MOSH-Insa-Toulouse/2025-2026-4GP-ZoeNonon-LouiseLammertyn-JilSaintMartin/1.Photos/Menu_du_capteur.jpg

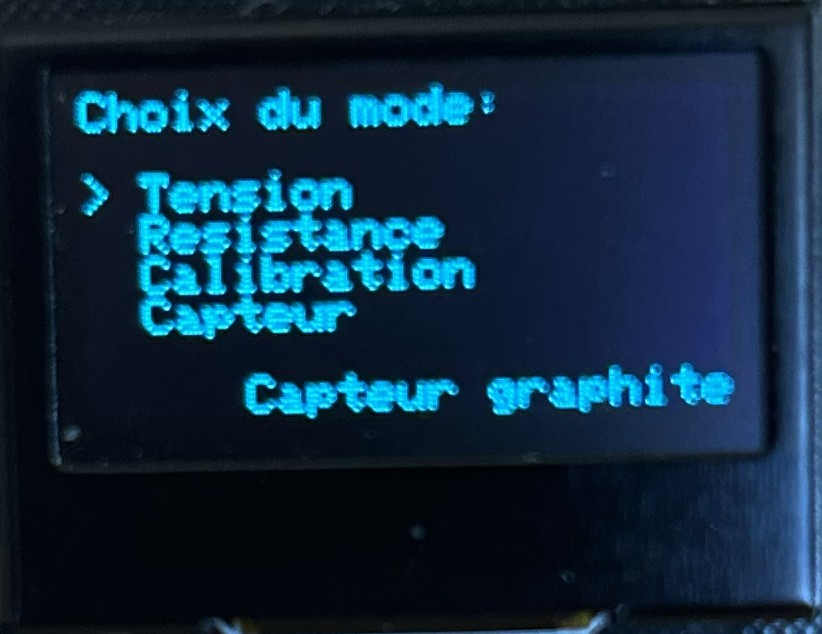
1.Photos/Menu_du_capteur.jpg
