MOSH-Insa-Toulouse/2025-2026-4GP-ZoeNonon-LouiseLammertyn-JilSaintMartin/2.LTSpice/capteur.png

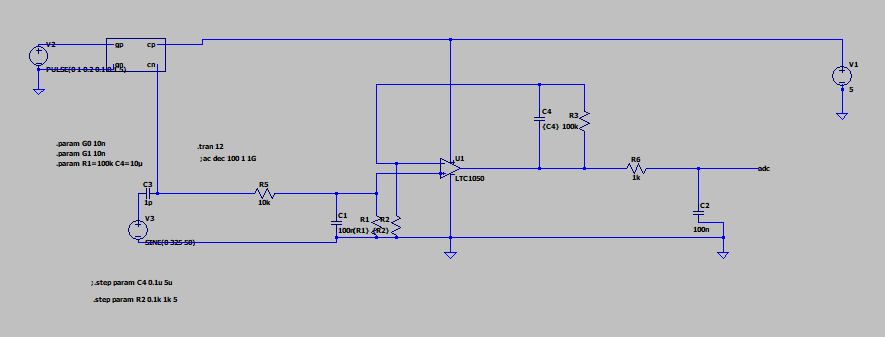
2.LTSpice/capteur.png
