MOSH-Insa-Toulouse/2025-2026-4GP-ZoeNonon-LouiseLammertyn-JilSaintMartin/5.Application/Lien_téléchargement.png

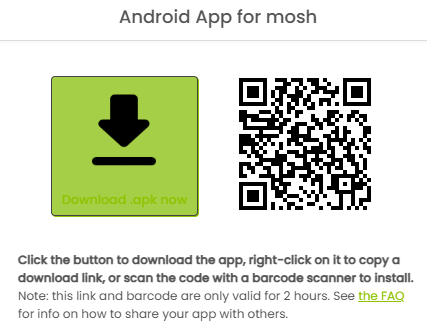
5.Application/Lien_téléchargement.png
