MOSH-Insa-Toulouse/2025-2026-4GP-ZoeNonon-LouiseLammertyn-JilSaintMartin/3.KiCad/Projet_capteur_pcb/Model 3d/pin-header-female-2-54mm-different-pin-numbers-1/10-Pin Header - Female - 2.54mm.step

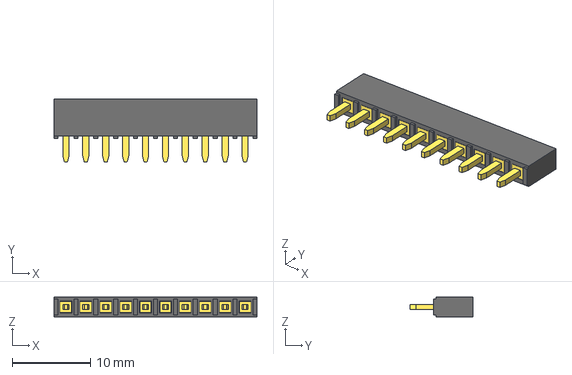
[picture p32: CAD file, 2026-04-08]
3.KiCad/Projet_capteur_pcb/Model 3d/pin-header-female-2-54mm-different-pin-numbers-1/10-Pin Header - Female - 2.54mm.step
25.9 x 8.00 x 2.50 mm
