MOSH-Insa-Toulouse/2025-2026-4GP-ZoeNonon-LouiseLammertyn-JilSaintMartin/1.Photos/Banc_de_test.png

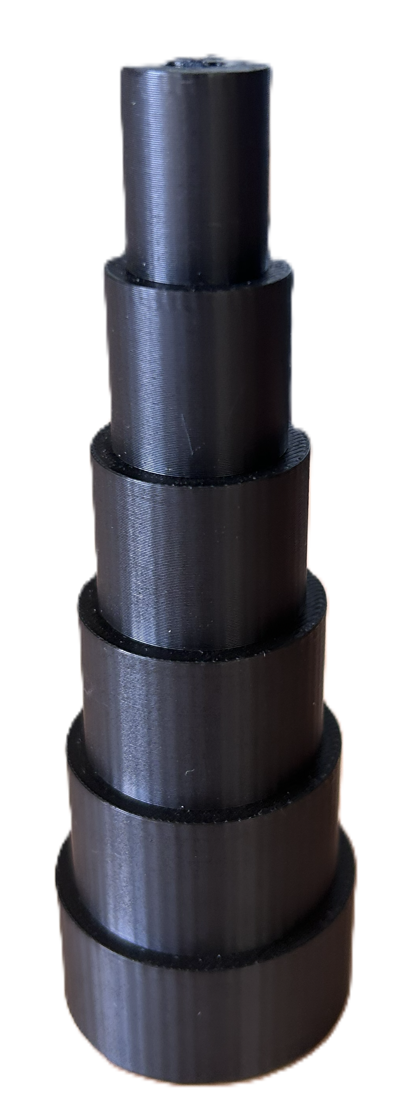
1.Photos/Banc_de_test.png
