MOSH-Insa-Toulouse/2025-2026-4GP-ZoeNonon-LouiseLammertyn-JilSaintMartin/Capteur_graphite.asc

B1: bi; I=v(cp,cn)*({G0}+{G1}*v(gc,gn))
C1: cap; 200µ
R1: res; 1k
Named nets: gp, gn, gc, cp, cn
