MOSH-Insa-Toulouse/2025-2026-4GP-ZoeNonon-LouiseLammertyn-JilSaintMartin/Draft2.asc

C1: cap; 0
C2: cap; 100n
C4: cap; 0
I1: current; PULSE(50n 100n 1 0.1 0.1 2); AC 1
R1: res; 100k
R2: res; 1k
R3: res; 100k
R5: res; 10k
R6: res; 1k
U1: LTC1050
V1: voltage; 5
Named nets: 0, adc
;tran 4
.ac dec 100 1 1G
