MOSH-Insa-Toulouse/2025-2026-4GP-ZoeNonon-LouiseLammertyn-JilSaintMartin/Schéma.asc

C1: cap; 100n
C2: cap; 100n
C3: cap; 1p
C4: cap; {C4}
R1: res; {R1}
R2: res; {R2}
R3: res; 100k
R5: res; 10k
R6: res; 1k
U1: LTC1050
V1: voltage; 5
V2: voltage; PULSE(0 1 0.2 0.1 0.1 5)
V3: voltage; SINE(0 325 50)
X5: Capteur_graphite
Named nets: 0, adc
.tran 12
;ac dec 100 1 1G
.param G0 10n
.param G1 10n
.param R1=100k C4=10µ
;.step param C4 0.1u 5u
.step param R2 0.1k 1k 5
